BK314159/Banchtop_NMR_STL_files/Sample holder and coil forms/Top frame.stl

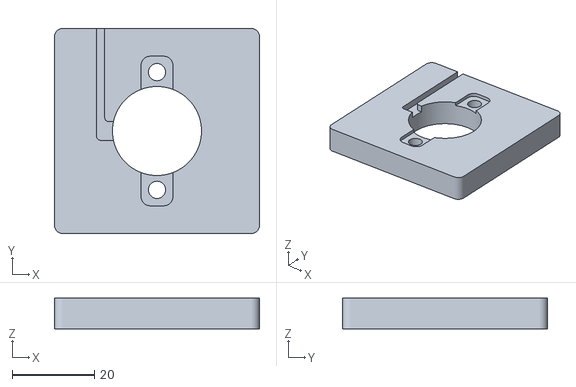
[picture p52: CAD file, 2026-08-17]
Sample holder and coil forms/Top frame.stl
50.0 x 50.0 x 7.50
